KNikolaich/Guitar-electric/Claude outputs/pcb_smd_preview.png

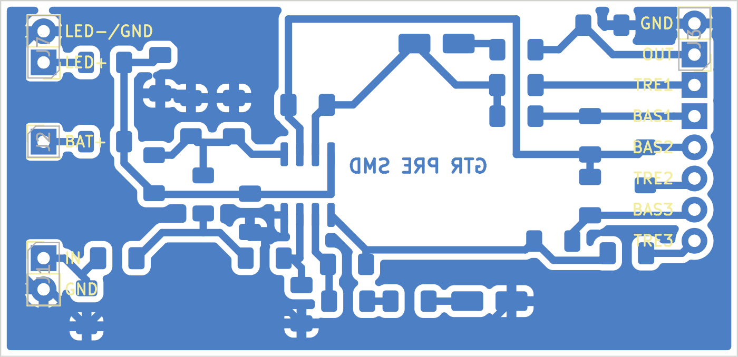
Claude outputs/pcb_smd_preview.png
