KNikolaich/Guitar-electric/etching/bottom_copper_preview.png

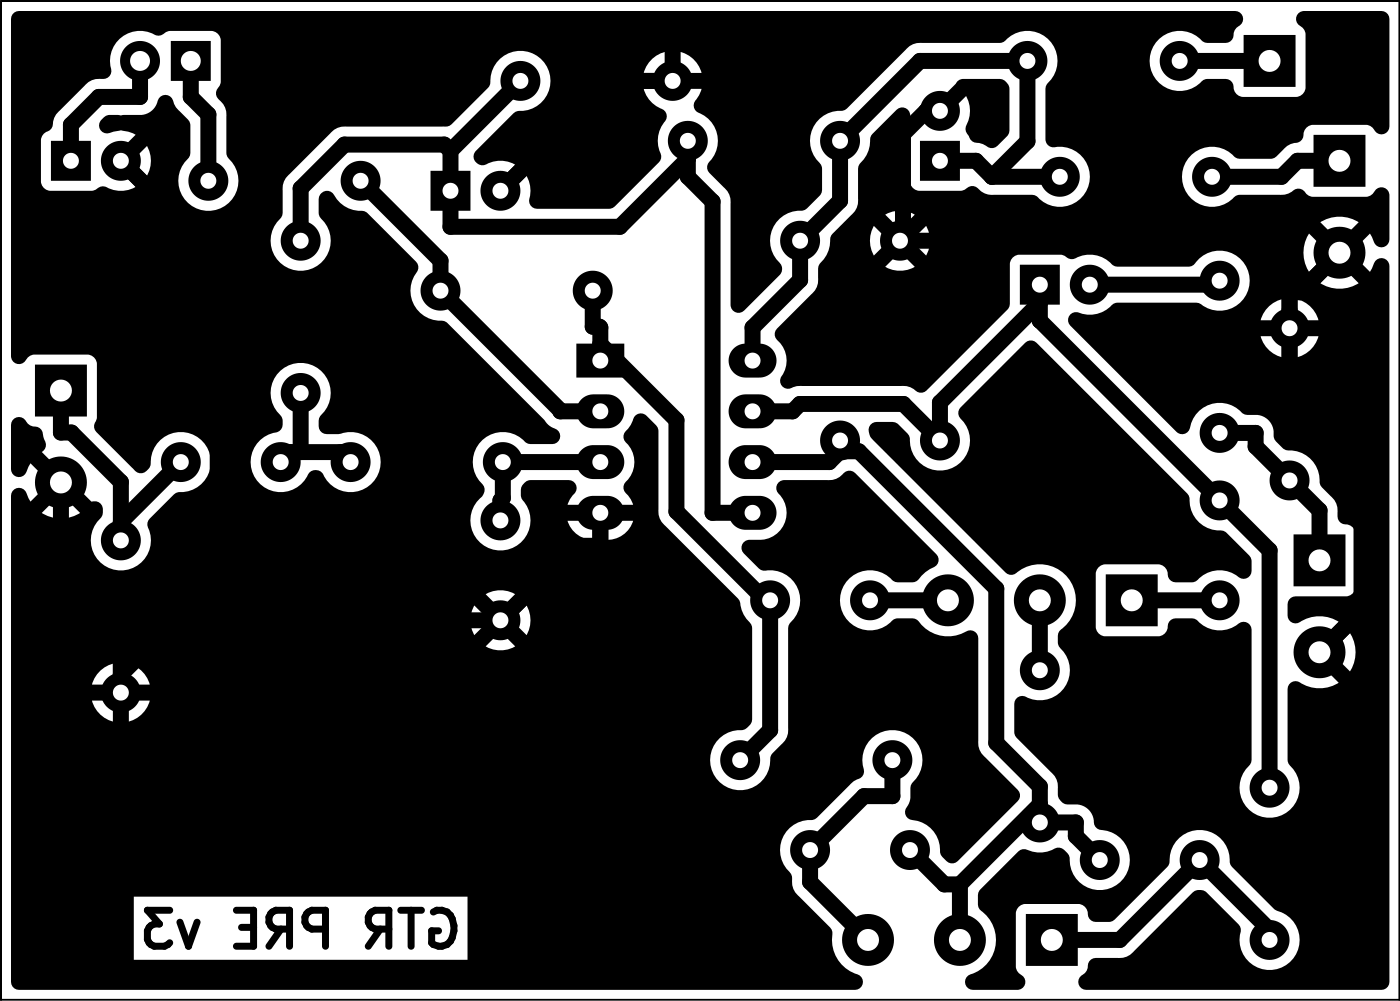
etching/bottom_copper_preview.png
