KNikolaich/Guitar-electric/etching_smd/bottom_copper_preview.png

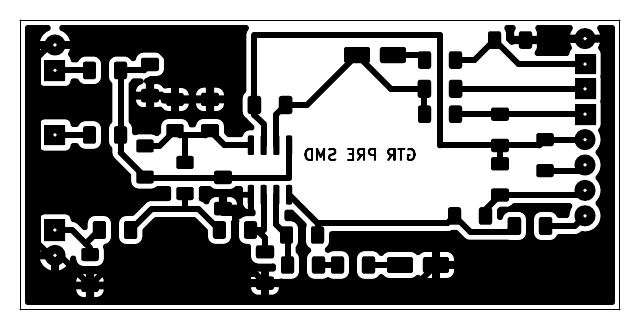
etching_smd/bottom_copper_preview.png
