KNikolaich/Guitar-electric/Claude outputs/perfboard_30x70_component_side.png

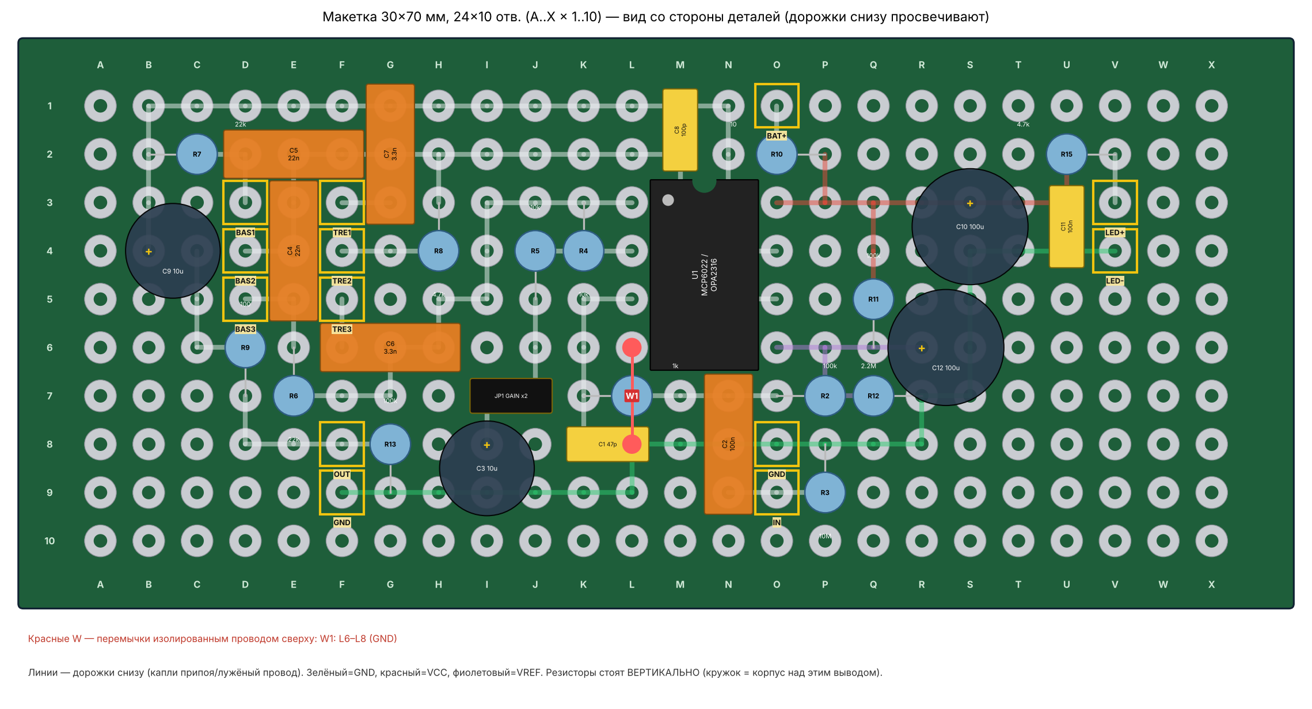
Claude outputs/perfboard_30x70_component_side.png
