KNikolaich/Guitar-electric/assembly_smd/assembly_copper_side_SMD.png

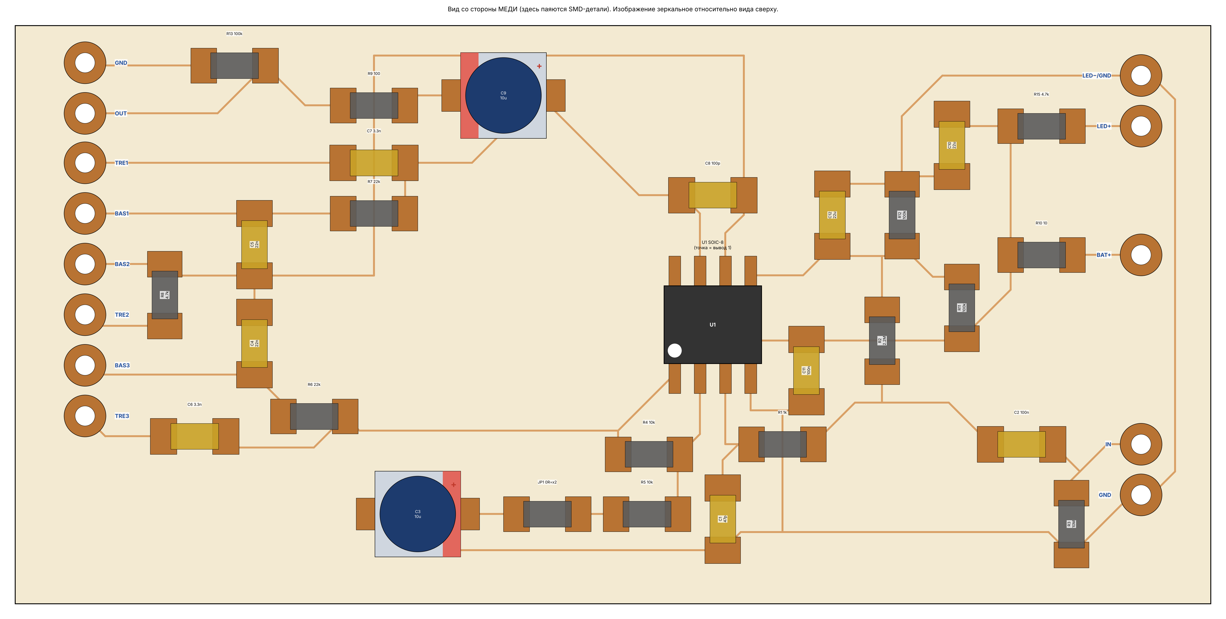
assembly_smd/assembly_copper_side_SMD.png
