KNikolaich/Guitar-electric/assembly_smd/wire_pads_top_side.png

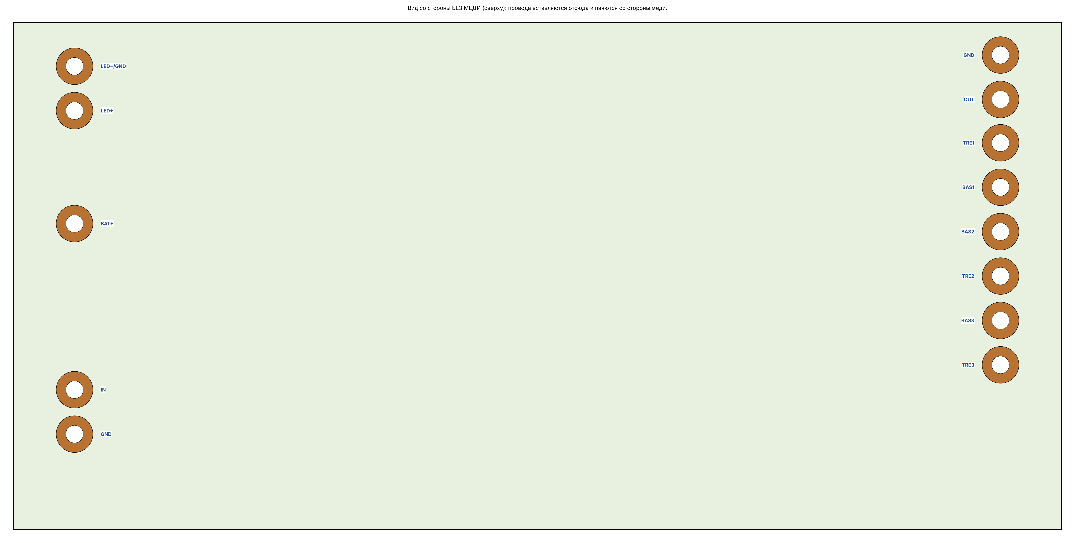
assembly_smd/wire_pads_top_side.png
