KNikolaich/Guitar-electric/perfboard/perfboard_30x70_solder_side_mirrored.png

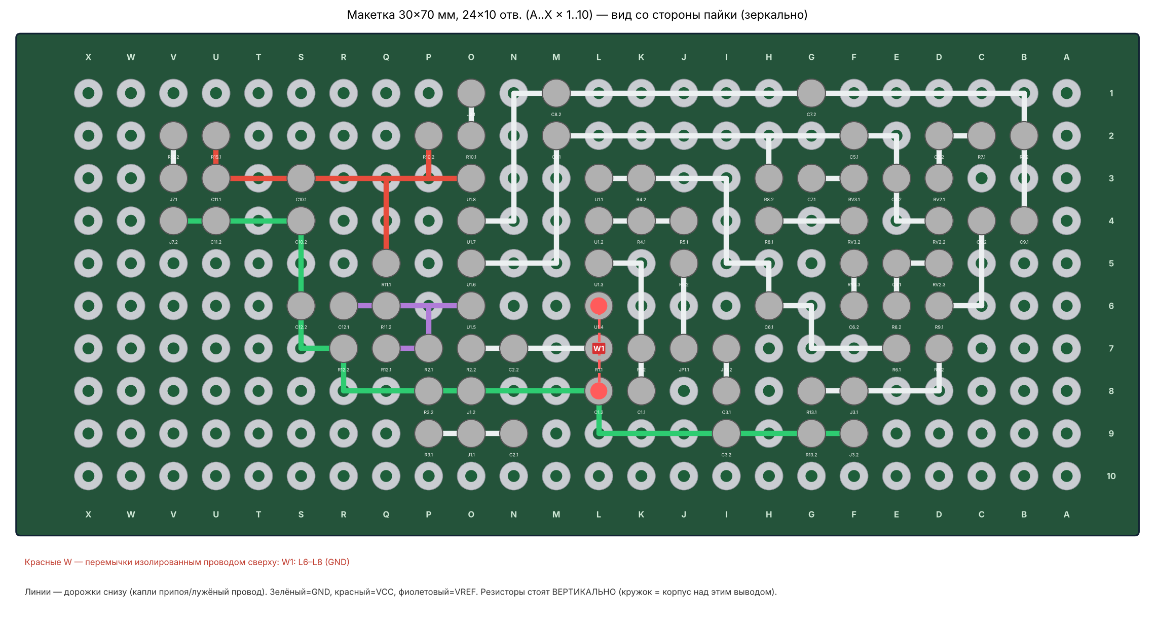
perfboard/perfboard_30x70_solder_side_mirrored.png
