KNikolaich/Guitar-electric/perfboard/perfboard_solder_side_mirrored.png

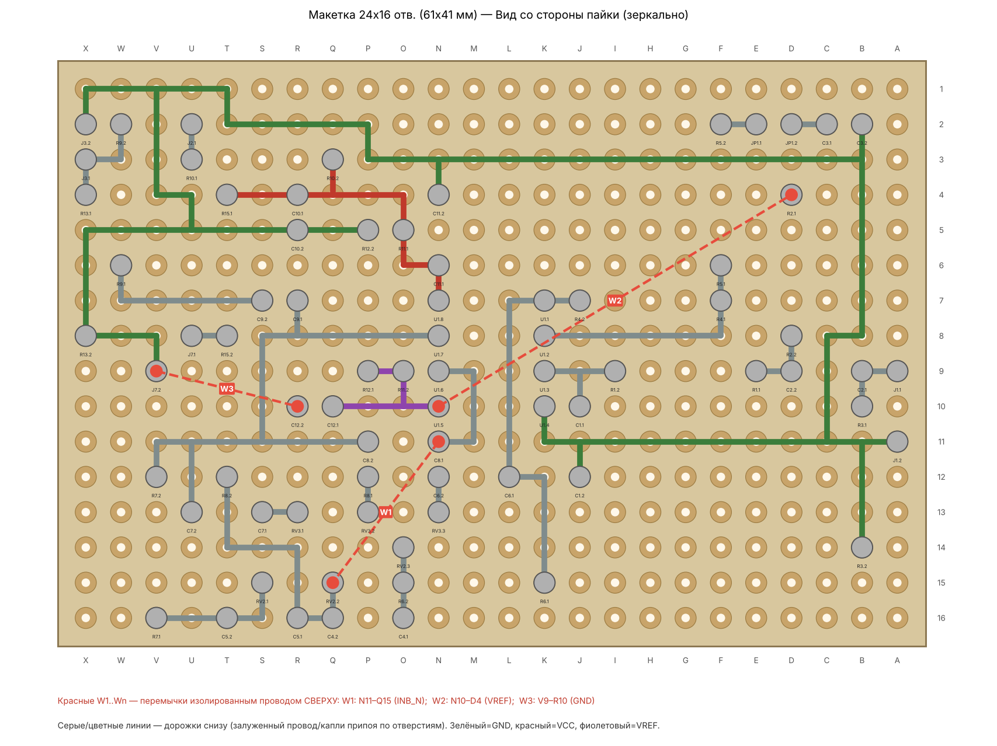
perfboard/perfboard_solder_side_mirrored.png
